OfficerPlotTwist/Mac_Mini_Wallmount/macmini-wall-mount/versions/v06b_blender-boolean-cut.stl

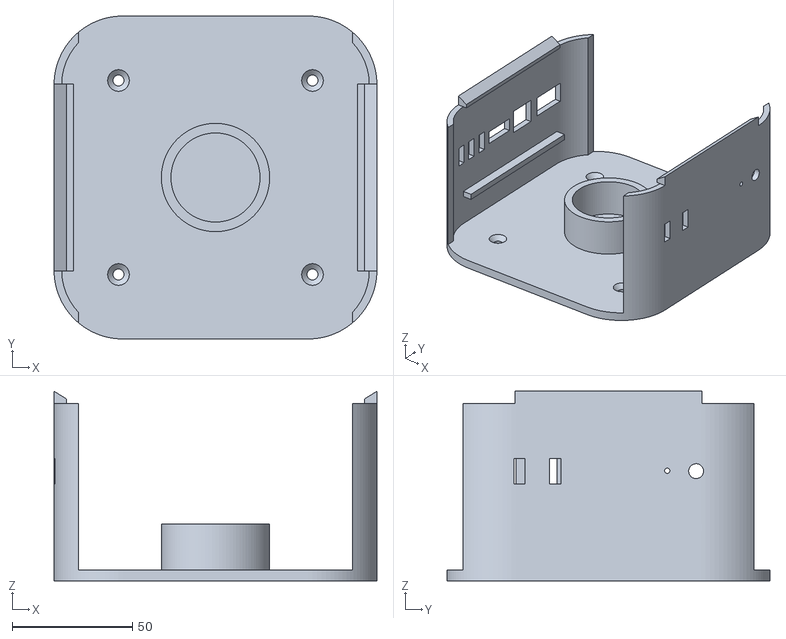
[picture p18: CAD file, 2026-06-18]
macmini-wall-mount/versions/v06b_blender-boolean-cut.stl
134.2 x 134.2 x 78.8
